scsd-cdh/tinywell/dashboard/src/colors.rs

use crate::Color32;

pub const COLOR_SLATE_100: Color32 = Color32::from_rgb(241, 245, 249);
pub const COLOR_SLATE_500: Color32 = Color32::from_rgb(100, 116, 139);
pub const COLOR_SLATE_600: Color32 = Color32::from_rgb(71, 85, 105);
pub const COLOR_SLATE_700: Color32 = Color32::from_rgb(51, 65, 85);
